cyclingProfessor/DriverlessCar/Bluno M3/500px-ADC.png

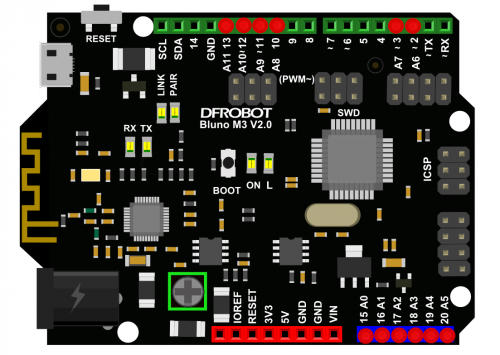
Bluno M3/500px-ADC.png
