cyclingProfessor/DriverlessCar/Bluno M3/600px-DFR0329_M3UART.png

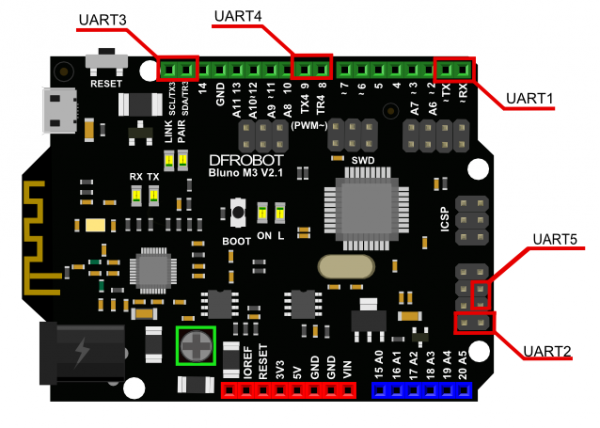
Bluno M3/600px-DFR0329_M3UART.png
