cyclingProfessor/DriverlessCar/Camera/CV2/rawImage.jpg

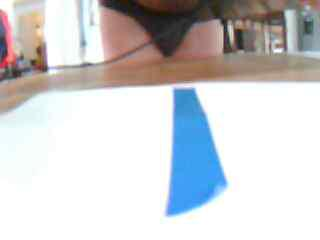
Camera/CV2/rawImage.jpg
