cyclingProfessor/DriverlessCar/Pictures/20171027_104113.jpg

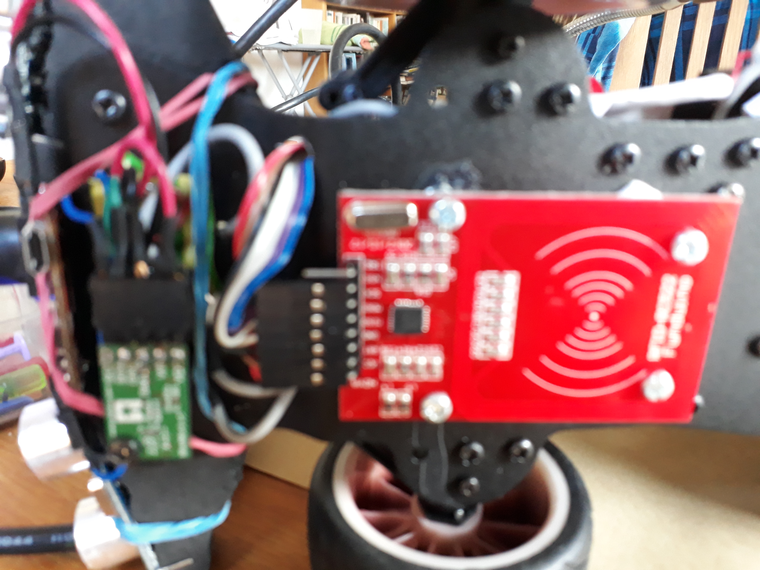
Pictures/20171027_104113.jpg
