cyclingProfessor/DriverlessCar/SDCard/SDCard.ino

/*
  SD card test

  This example shows how use the utility libraries on which the'
  SD library is based in order to get info about your SD card.
  Very useful for testing a card when you're not sure whether its working or not.

  The circuit:
    SD card attached to SPI bus as follows:
 ** MOSI - pin 11 on Arduino Uno/Duemilanove/Diecimila
 ** MISO - pin 12 on Arduino Uno/Duemilanove/Diecimila
 ** CLK - pin 13 on Arduino Uno/Duemilanove/Diecimila
 ** CS - depends on your SD card shield or module.
        Pin 4 used here for consistency with other Arduino examples


  created  28 Mar 2011
  by Limor Fried
  modified 9 Apr 2012
  by Tom Igoe
*/
// include the SD library:
#include <SPI.h>
#include <SD.h>

// set up variables using the SD utility library functions:
Sd2Card card;
SdVolume volume;
SdFile root;

// change this to match your SD shield or module;
// Arduino Ethernet shield: pin 4
// Adafruit SD shields and modules: pin 10
// Sparkfun SD shield: pin 8
// MKRZero SD: SDCARD_SS_PIN
const int chipSelect = 31;

void setup() {
  // Open serial communications and wait for port to open:
  Serial1.begin(115200);
  while (!Serial1) {
    ; // wait for serial port to connect. Needed for native USB port only
  }


  Serial1.print("\nInitializing SD card...");

  // we'll use the initialization code from the utility libraries
  // since we're just testing if the card is working!
  if (!card.init(SPI_HALF_SPEED, chipSelect)) {
    Serial1.println("initialization failed. Things to check:");
    Serial1.println("* is a card inserted?");
    Serial1.println("* is your wiring correct?");
    Serial1.println("* did you change the chipSelect pin to match your shield or module?");
    while (1);
  } else {
    Serial1.println("Wiring is correct and a card is present.");
  }

  // print the type of card
  Serial1.println();
  Serial1.print("Card type:         ");
  switch (card.type()) {
    case SD_CARD_TYPE_SD1:
      Serial1.println("SD1");
      break;
    case SD_CARD_TYPE_SD2:
      Serial1.println("SD2");
      break;
    case SD_CARD_TYPE_SDHC:
      Serial1.println("SDHC");
      break;
    default:
      Serial1.println("Unknown");
  }

  // Now we will try to open the 'volume'/'partition' - it should be FAT16 or FAT32
  if (!volume.init(card)) {
    Serial1.println("Could not find FAT16/FAT32 partition.\nMake sure you've formatted the card");
    while (1);
  }

  Serial1.print("Clusters:          ");
  Serial1.println(volume.clusterCount());
  Serial1.print("Blocks x Cluster:  ");
  Serial1.println(volume.blocksPerCluster());

  Serial1.print("Total Blocks:      ");
  Serial1.println(volume.blocksPerCluster() * volume.clusterCount());
  Serial1.println();

  // print the type and size of the first FAT-type volume
  uint32_t volumesize;
  Serial1.print("Volume type is:    FAT");
  Serial1.println(volume.fatType(), DEC);

  volumesize = volume.blocksPerCluster();    // clusters are collections of blocks
  volumesize *= volume.clusterCount();       // we'll have a lot of clusters
  volumesize /= 2;                           // SD card blocks are always 512 bytes (2 blocks are 1KB)
  Serial1.print("Volume size (Kb):  ");
  Serial1.println(volumesize);
  Serial1.print("Volume size (Mb):  ");
  volumesize /= 1024;
  Serial1.println(volumesize);
  Serial1.print("Volume size (Gb):  ");
  Serial1.println((float)volumesize / 1024.0);

  Serial1.println("\nFiles found on the card (name, date and size in bytes): ");
  root.openRoot(volume);
  

  // list all files in the card with date and size
  root.ls(LS_R | LS_DATE | LS_SIZE);
}

void loop(void) {
}
