cyclingProfessor/DriverlessCar/Camera/Arduino/ReadAsMaster/ReadAsMaster.ino

#include <Wire.h>
#define BAUD_RATE 115200
#define CHAR_BUF 128
#define GET_VALUE 0
#define CALIBRATE 1
#define CAMERA_PIN 8

int mode = CALIBRATE;
void setup() {
  Serial.begin(BAUD_RATE);
  Wire.begin();
  pinMode(CAMERA_PIN, OUTPUT);
  digitalWrite(CAMERA_PIN, LOW);
  Serial.println("In Calibrate mode.  Type 0 to read line on the camera.");
  delay(1000); // Give the OpenMV Cam time to bootup.
}

// This needs careful timeout management.
void loop() {
  if (Serial.available() > 0) {
    int inByte = Serial.read();

    switch (inByte) {
      case '0':
        digitalWrite(CAMERA_PIN, HIGH);
        mode = GET_VALUE;
        Serial.println("Mode set to read camera - look for read, white, green and magenta as the car is moved.");
        break;
      case '1':
        digitalWrite(CAMERA_PIN, LOW);
        mode = CALIBRATE;
        Serial.println("Mode set to calibrate - look for Blue flashing changing  to Blue when it finds the line.");
        break;
      case 'h':
      default:
        Serial.println("Type 0 to read line or 1 to calibrate the camera.");
        break;
    }
  }
  if (mode == GET_VALUE) {
    Serial.println("Asking for data");
    Serial.println(Wire.requestFrom(0x12, 1));
    Serial.println("Got some data");
    if(Wire.available()) {
        Serial.println(Wire.read());
    }
  }
  delay(100); // Don't loop to quickly.
  Serial.println(millis());
}
